greigs/OpenBrickGB/3D Printed Parts/cone.stl

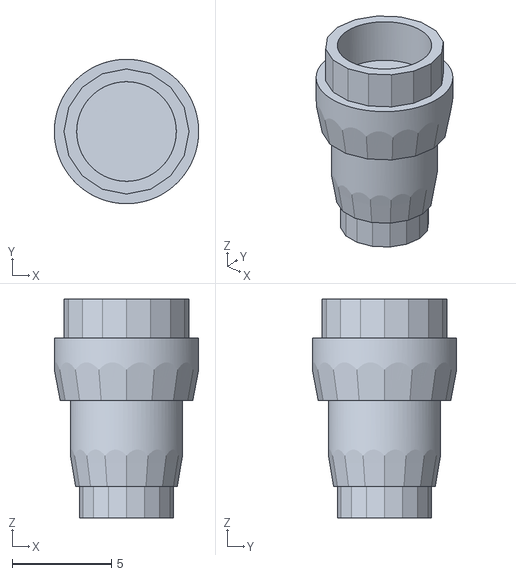
[picture p17: CAD file, 2026-06-02]
3D Printed Parts/cone.stl
7.27 x 7.27 x 11.0
