greigs/OpenBrickGB/3D Printed Parts/actuator.stl

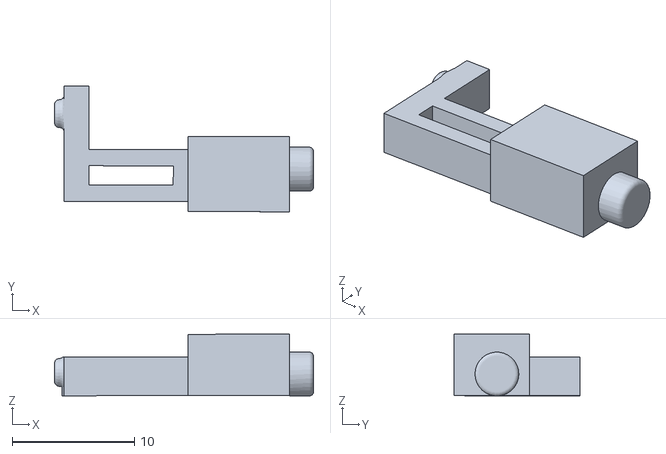
[picture p18: CAD file, 2026-06-02]
3D Printed Parts/actuator.stl
21.2 x 10.3 x 5.04
