greigs/OpenBrickGB/Main PCB/Kicad Components/450404015514/450404015514.step

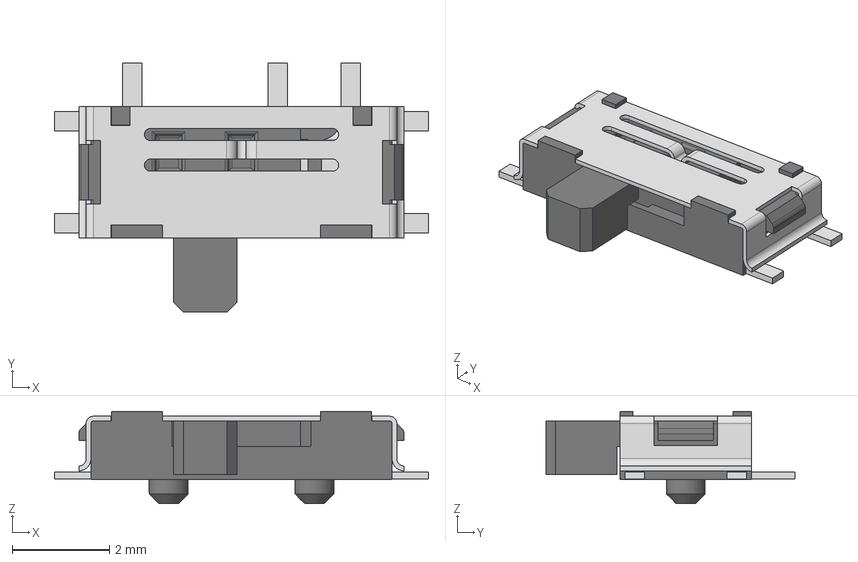
[picture p19: CAD file, 2025-10-12]
Main PCB/Kicad Components/450404015514/450404015514.step
7.70 x 5.13 x 1.90 mm
Frame
Pin 4
Frame 1
Pin 1
Pin 2
Pin 3
Slider 1
Slider
Cover
