greigs/OpenBrickGB/Main PCB/Kicad Components/BQ24040DSQR/BQ24040DSQR.step

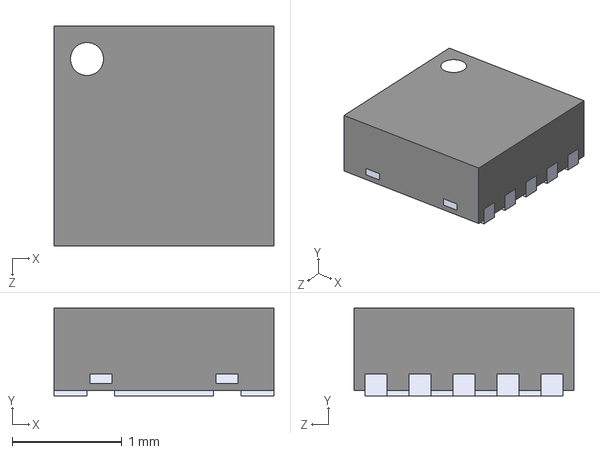
[picture p20: CAD file, 2025-10-12]
Main PCB/Kicad Components/BQ24040DSQR/BQ24040DSQR.step
2.00 x 0.8 x 2.00 mm
